akornsys-rdi/open-wound/brd/master/audio-sensing-board/audio.sch

## KiCad design brd/master/audio-sensing-board/audio.sch (2015-06-30)

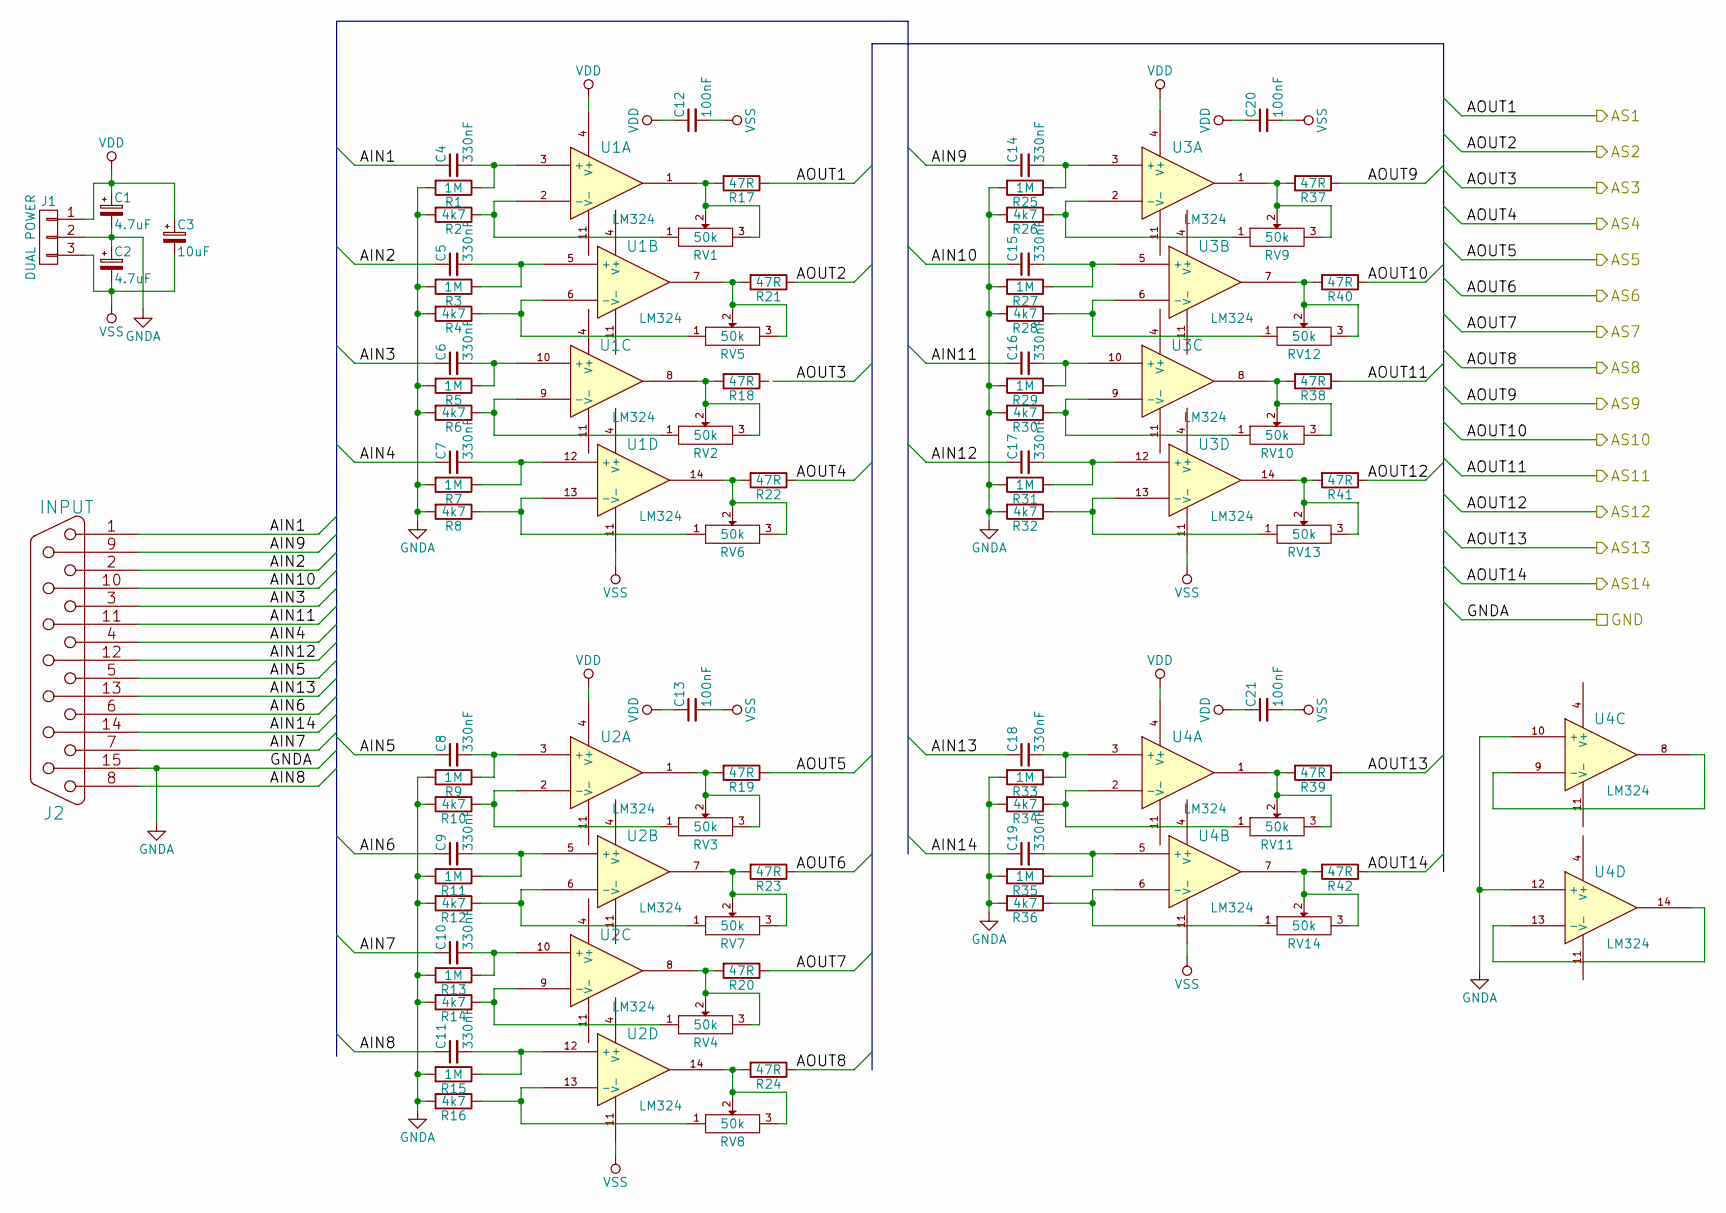
[picture p10: schematic audio.sch]

Parts:
C1, C2: 4.7uF
C3: 10uF
C4, C5, C6, C7, C8, C9, C10, C11, C14, C15, C16, C17, C18, C19: 330nF
C12, C13, C20, C21: 100nF
J1: DUAL POWER
J2: INPUT
R1, R3, R5, R7, R9, R11, R13, R15, R25, R27, R29, R31, R33, R35: 1M
R2, R4, R6, R8, R10, R12, R14, R16, R26, R28, R30, R32, R34, R36: 4k7
R17, R18, R19, R20, R21, R22, R23, R24, R37, R38, R39, R40, R41, R42: 47R
RV1, RV2, RV3, RV4, RV5, RV6, RV7, RV8, RV9, RV10, RV11, RV12, RV13, RV14: 50k
U1, U2, U3, U4: LM324

Connections:
AIN1: C4.1, J2.1
AIN2: C5.1, J2.2
AIN3: C6.1, J2.3
AIN4: C7.1, J2.4
AIN5: C8.1, J2.5
AIN6: C9.1, J2.6
AIN7: C10.1, J2.7
AIN8: C11.1, J2.8
AIN9: C14.1, J2.9
AIN10: C15.1, J2.10
AIN11: C16.1, J2.11 (P111)
AIN12: C17.1, J2.12
AIN13: C18.1, J2.13
AIN14: C19.1, J2.14
AOUT1: R17.1
AOUT2: R21.1
AOUT4: R22.1
AOUT5: R19.1
AOUT6: R23.1
AOUT7: R20.1
AOUT8: R24.1
AOUT9: R37.1
AOUT10: R40.1
AOUT11: R38.1
AOUT12: R41.1
AOUT13: R39.1
AOUT14: R42.1
GNDA: C1.2, C2.1, J1.2, J2.15, R1.2, R2.2, R3.2, R4.2, R5.2, R6.2, R7.2, R8.2, R9.2, R10.2, R11.2, R12.2, R13.2, R14.2, R15.2, R16.2, R25.2, R26.2, R27.2, R28.2, R29.2, R30.2, R31.2, R32.2, R33.2, R34.2, R35.2, R36.2, U4.10 (+), U4.12 (+)
unnamed: C4.2, R1.1, U1.3 (+)
unnamed: C5.2, R3.1, U1.5 (+)
unnamed: C6.2, R5.1, U1.10 (+)
unnamed: C7.2, R7.1, U1.12 (+)
unnamed: C8.2, R9.1, U2.3 (+)
unnamed: C9.2, R11.1, U2.5 (+)
unnamed: C10.2, R13.1, U2.10 (+)
unnamed: C11.2, R15.1, U2.12 (+)
unnamed: C14.2, R25.1, U3.3 (+)
unnamed: C15.2, R27.1, U3.5 (+)
unnamed: C16.2, R29.1, U3.10 (+)
unnamed: C17.2, R31.1, U3.12 (+)
unnamed: C18.2, R33.1, U4.3 (+)
unnamed: C19.2, R35.1, U4.5 (+)
unnamed: R2.1, RV1.1, U1.2 (-)
unnamed: R4.1, RV5.1, U1.6 (-)
unnamed: R6.1, RV2.1, U1.9 (-)
unnamed: R8.1, RV6.1, U1.13 (-)
unnamed: R10.1, RV3.1, U2.2 (-)
unnamed: R12.1, RV7.1, U2.6 (-)
unnamed: R14.1, RV4.1, U2.9 (-)
unnamed: R16.1, RV8.1, U2.13 (-)
unnamed: R17.2, RV1.2, RV1.3, U1.1
unnamed: R18.2, RV2.2, RV2.3, U1.8
unnamed: R19.2, RV3.2, RV3.3, U2.1
unnamed: R20.2, RV4.2, RV4.3, U2.8
unnamed: R21.2, RV5.2, RV5.3, U1.7
unnamed: R22.2, RV6.2, RV6.3, U1.14
unnamed: R23.2, RV7.2, RV7.3, U2.7
unnamed: R24.2, RV8.2, RV8.3, U2.14
unnamed: R26.1, RV9.1, U3.2 (-)
unnamed: R28.1, RV12.1, U3.6 (-)
unnamed: R30.1, RV10.1, U3.9 (-)
unnamed: R32.1, RV13.1, U3.13 (-)
unnamed: R34.1, RV11.1, U4.2 (-)
unnamed: R36.1, RV14.1, U4.6 (-)
unnamed: R37.2, RV9.2, RV9.3, U3.1
unnamed: R38.2, RV10.2, RV10.3, U3.8
unnamed: R39.2, RV11.2, RV11.3, U4.1
unnamed: R40.2, RV12.2, RV12.3, U3.7
unnamed: R41.2, RV13.2, RV13.3, U3.14
unnamed: R42.2, RV14.2, RV14.3, U4.7
unnamed: U4.8, U4.9 (-)
unnamed: U4.13 (-), U4.14
VDD: C1.1, C3.1, C12.1, C13.1, C20.1, C21.1, J1.1, U1.4 (V+), U2.4 (V+), U3.4 (V+), U4.4 (V+)
VSS: C2.2, C3.2, C12.2, C13.2, C20.2, C21.2, J1.3, U1.11 (V-), U2.11 (V-), U3.11 (V-), U4.11 (V-)
