akornsys-rdi/open-wound/brd/master/audio-sensing-board/digital.sch

## KiCad design brd/master/audio-sensing-board/digital.sch (2015-06-30)

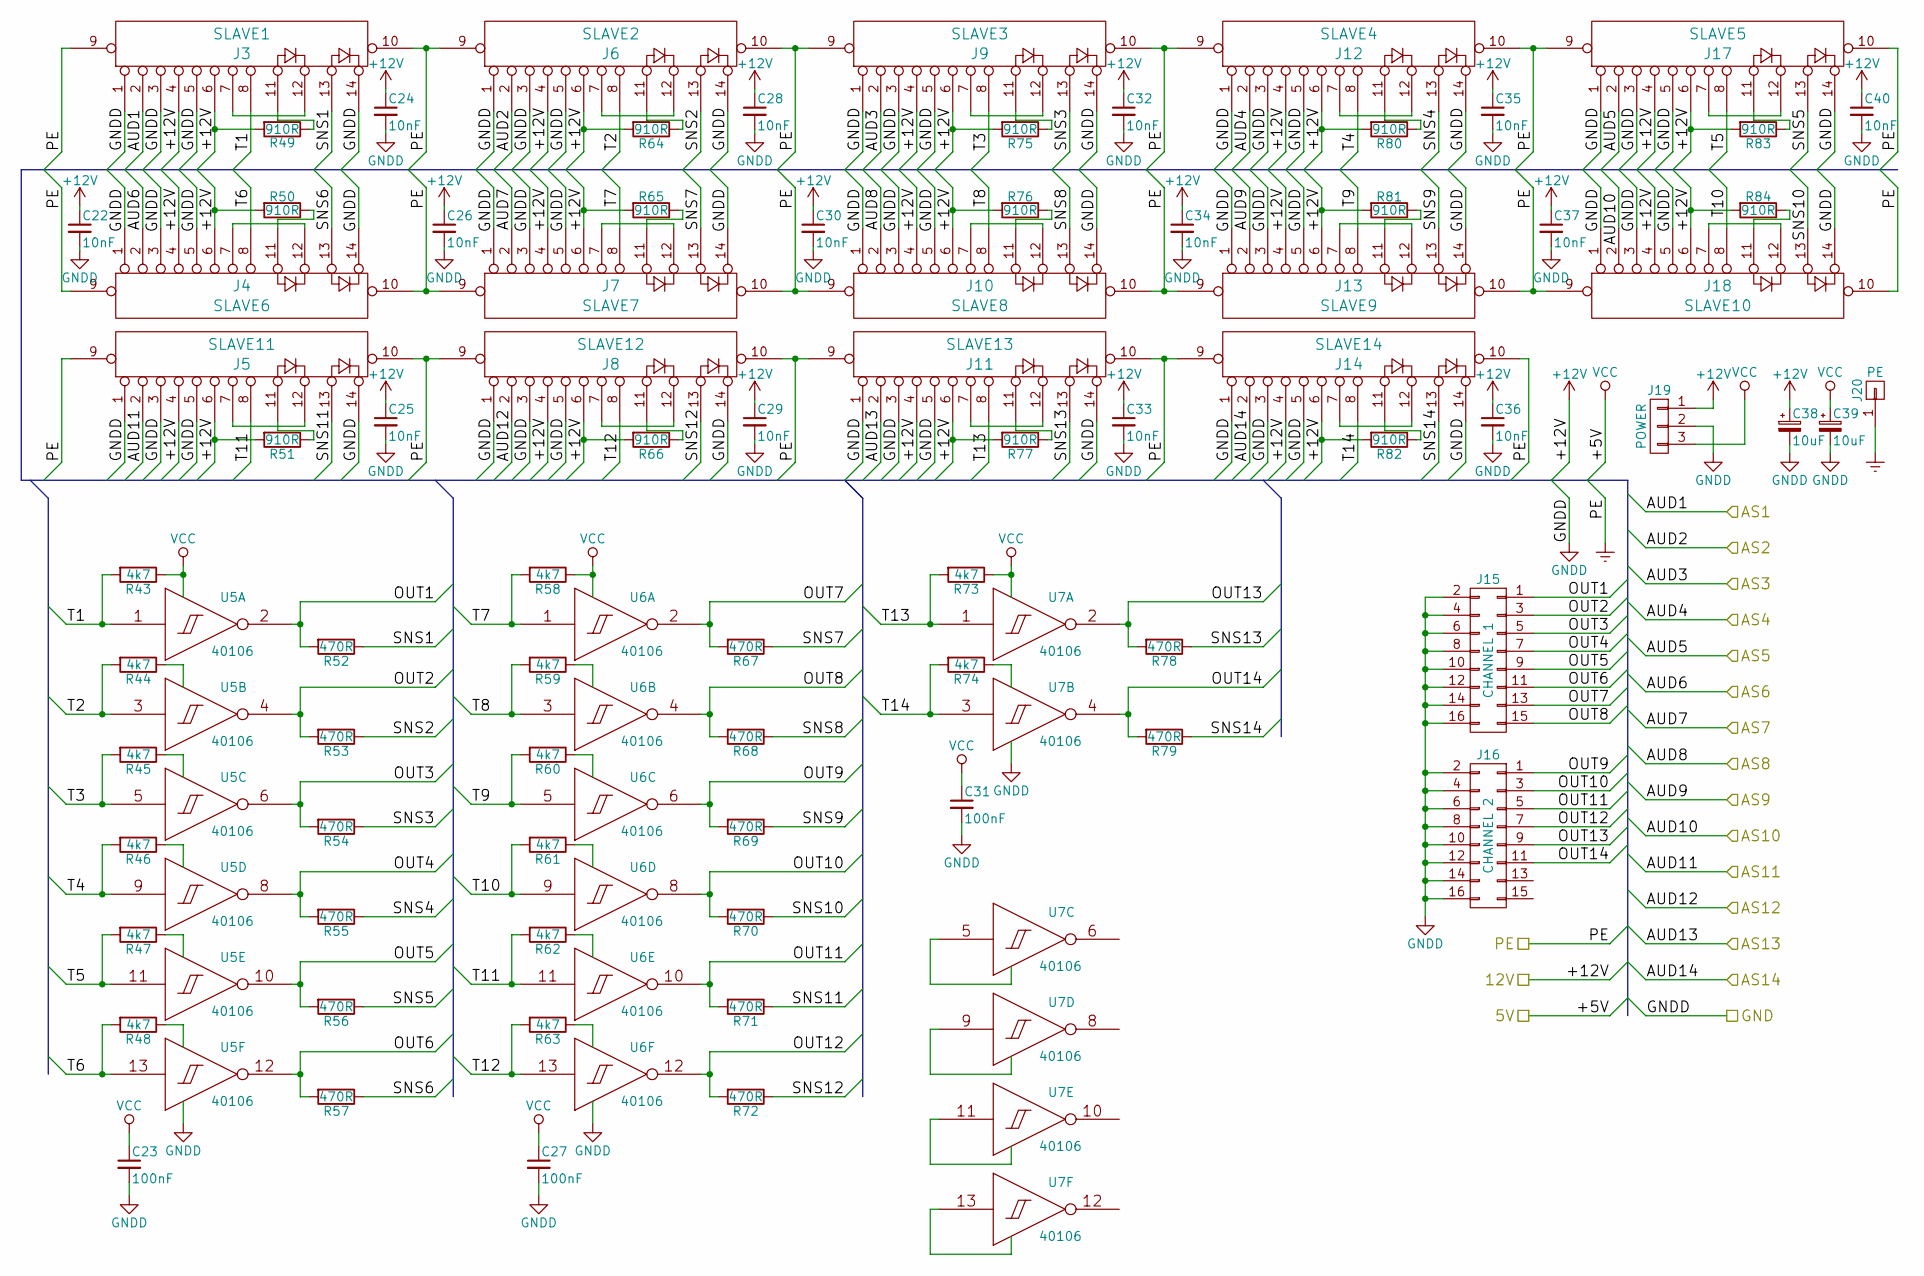
[picture p11: schematic digital.sch]

Parts:
C22, C24, C25, C26, C28, C29, C30, C32, C33, C34, C35, C36, C37, C40: 10nF
C23, C27, C31: 100nF
C38, C39: 10uF
J3: SLAVE1
J4: SLAVE6
J5: SLAVE11
J6: SLAVE2
J7: SLAVE7
J8: SLAVE12
J9: SLAVE3
J10: SLAVE8
J11: SLAVE13
J12: SLAVE4
J13: SLAVE9
J14: SLAVE14
J15: CHANNEL 1
J16: CHANNEL 2
J17: SLAVE5
J18: SLAVE10
J19: POWER
J20: PE
R43, R44, R45, R46, R47, R48, R58, R59, R60, R61, R62, R63, R73, R74: 4k7
R49, R50, R51, R64, R65, R66, R75, R76, R77, R80, R81, R82, R83, R84: 910R
R52, R53, R54, R55, R56, R57, R67, R68, R69, R70, R71, R72, R78, R79: 470R
U5, U6, U7: 40106

Connections:
+12V: C22.1, C24.1, C25.1, C26.1, C28.1, C29.1, C30.1, C32.1, C33.1, C34.1, C35.1, C36.1, C37.1, C38.1, C40.1, J3.4, J3.6, J4.4, J4.6, J5.4, J5.6, J6.4, J6.6, J7.4, J7.6, J8.4, J8.6, J9.4, J9.6, J10.4, J10.6, J11.4, J11.6, J12.4, J12.6, J13.4, J13.6, J14.4, J14.6, J17.4, J17.6, J18.4, J18.6, J19.1, R49.2, R50.2, R51.2, R64.2, R65.2, R66.2, R75.2, R76.2, R77.2, R80.2, R81.2, R82.2, R83.2, R84.2
AS1: J3.2
AS2: J6.2
AS3: J9.2
AS4: J12.2
AS5: J17.2
AS6: J4.2
AS7: J7.2
AS8: J10.2
AS9: J13.2
AS10: J18.2
AS11: J5.2
AS12: J8.2
AS13: J11.2
AS14: J14.2
Earth: J3.9, J3.10, J4.9, J4.10, J5.9, J5.10, J6.9, J6.10, J7.9, J7.10, J8.9, J8.10, J9.9, J9.10, J10.9, J10.10, J11.9, J11.10, J12.9, J12.10, J13.9, J13.10, J14.9, J14.10, J17.9, J17.10, J18.9, J18.10, J20.1
GNDD: C22.2, C23.2, C24.2, C25.2, C26.2, C27.2, C28.2, C29.2, C30.2, C31.2, C32.2, C33.2, C34.2, C35.2, C36.2, C37.2, C38.2, C39.2, C40.2, J3.1, J3.3, J3.5, J3.14, J4.1, J4.3, J4.5, J4.14, J5.1, J5.3, J5.5, J5.14, J6.1, J6.3, J6.5, J6.14, J7.1, J7.3, J7.5, J7.14, J8.1, J8.3, J8.5, J8.14, J9.1, J9.3, J9.5, J9.14, J10.1, J10.3, J10.5, J10.14, J11.1, J11.3, J11.5, J11.14, J12.1, J12.3, J12.5, J12.14, J13.1, J13.3, J13.5, J13.14, J14.1, J14.3, J14.5, J14.14, J15.2, J15.4, J15.6, J15.8, J15.10, J15.12, J15.14, J15.16, J16.2, J16.4, J16.6, J16.8, J16.10, J16.12, J16.14, J16.16, J17.1, J17.3, J17.5, J17.14, J18.1, J18.3, J18.5, J18.14, J19.2, U5.7 (VSS), U6.7 (VSS), U7.7 (VSS)
unnamed: J3.11, R49.1
unnamed: J3.7, J3.12
unnamed: J4.11, R50.1
unnamed: J4.7, J4.12
unnamed: J5.11, R51.1
unnamed: J5.7, J5.12
unnamed: J6.11, R64.1
unnamed: J6.7, J6.12
unnamed: J7.11, R65.1
unnamed: J7.7, J7.12
unnamed: J8.11, R66.1
unnamed: J8.7, J8.12
unnamed: J9.11, R75.1
unnamed: J9.7, J9.12
unnamed: J10.11, R76.1
unnamed: J10.7, J10.12
unnamed: J11.11, R77.1
unnamed: J11.7, J11.12
unnamed: J12.11, R80.1
unnamed: J12.7, J12.12
unnamed: J13.11, R81.1
unnamed: J13.7, J13.12
unnamed: J14.11, R82.1
unnamed: J14.7, J14.12
unnamed: J17.11, R83.1
unnamed: J17.7, J17.12
unnamed: J18.11, R84.1
unnamed: J18.7, J18.12
unnamed: R44.1, U5.14 (VDD)
unnamed: R45.1, U5.14 (VDD)
unnamed: R46.1, U5.14 (VDD)
unnamed: R47.1, U5.14 (VDD)
unnamed: R48.1, U5.14 (VDD)
unnamed: R59.1, U6.14 (VDD)
unnamed: R60.1, U6.14 (VDD)
unnamed: R61.1, U6.14 (VDD)
unnamed: R62.1, U6.14 (VDD)
unnamed: R63.1, U6.14 (VDD)
unnamed: R74.1, U7.14 (VDD)
unnamed: U7.5 (In), U7.7 (VSS)
unnamed: U7.7 (VSS), U7.9 (In)
unnamed: U7.7 (VSS), U7.11 (In)
unnamed: U7.7 (VSS), U7.13 (In)
OUT1: J15.1, R52.2, U5.2 (Out)
OUT2: J15.3, R53.2, U5.4 (Out)
OUT3: J15.5, R54.2, U5.6 (Out)
OUT4: J15.7, R55.2, U5.8 (Out)
OUT5: J15.9, R56.2, U5.10 (Out)
OUT6: J15.11, R57.2, U5.12 (Out)
OUT7: J15.13, R67.2, U6.2 (Out)
OUT8: J15.15, R68.2, U6.4 (Out)
OUT9: J16.1, R69.2, U6.6 (Out)
OUT10: J16.3, R70.2, U6.8 (Out)
OUT11: J16.5, R71.2, U6.10 (Out)
OUT12: J16.7, R72.2, U6.12 (Out)
OUT13: J16.9, R78.2, U7.2 (Out)
OUT14: J16.11, R79.2, U7.4 (Out)
SNS1: J3.13, R52.1
SNS2: J6.13, R53.1
SNS3: J9.13, R54.1
SNS4: J12.13, R55.1
SNS5: J17.13, R56.1
SNS6: J4.13, R57.1
SNS7: J7.13, R67.1
SNS8: J10.13, R68.1
SNS9: J13.13, R69.1
SNS10: J18.13, R70.1
SNS11: J5.13, R71.1
SNS12: J8.13, R72.1
SNS13: J11.13, R78.1
SNS14: J14.13, R79.1
T1: J3.8, R43.2, U5.1 (In)
T2: J6.8, R44.2, U5.3 (In)
T3: J9.8, R45.2, U5.5 (In)
T4: J12.8, R46.2, U5.9 (In)
T5: J17.8, R47.2, U5.11 (In)
T6: J4.8, R48.2, U5.13 (In)
T7: J7.8, R58.2, U6.1 (In)
T8: J10.8, R59.2, U6.3 (In)
T9: J13.8, R60.2, U6.5 (In)
T10: J18.8, R61.2, U6.9 (In)
T11: J5.8, R62.2, U6.11 (In)
T12: J8.8, R63.2, U6.13 (In)
T13: J11.8, R73.2, U7.1 (In)
T14: J14.8, R74.2, U7.3 (In)
VCC: C23.1, C27.1, C31.1, C39.1, J19.3, R43.1, R58.1, R73.1, U5.14 (VDD), U6.14 (VDD), U7.14 (VDD)
