akornsys-rdi/open-wound/brd/master/audio-sensing-board/pir.sch

## KiCad design brd/master/audio-sensing-board/pir.sch (2015-06-30)

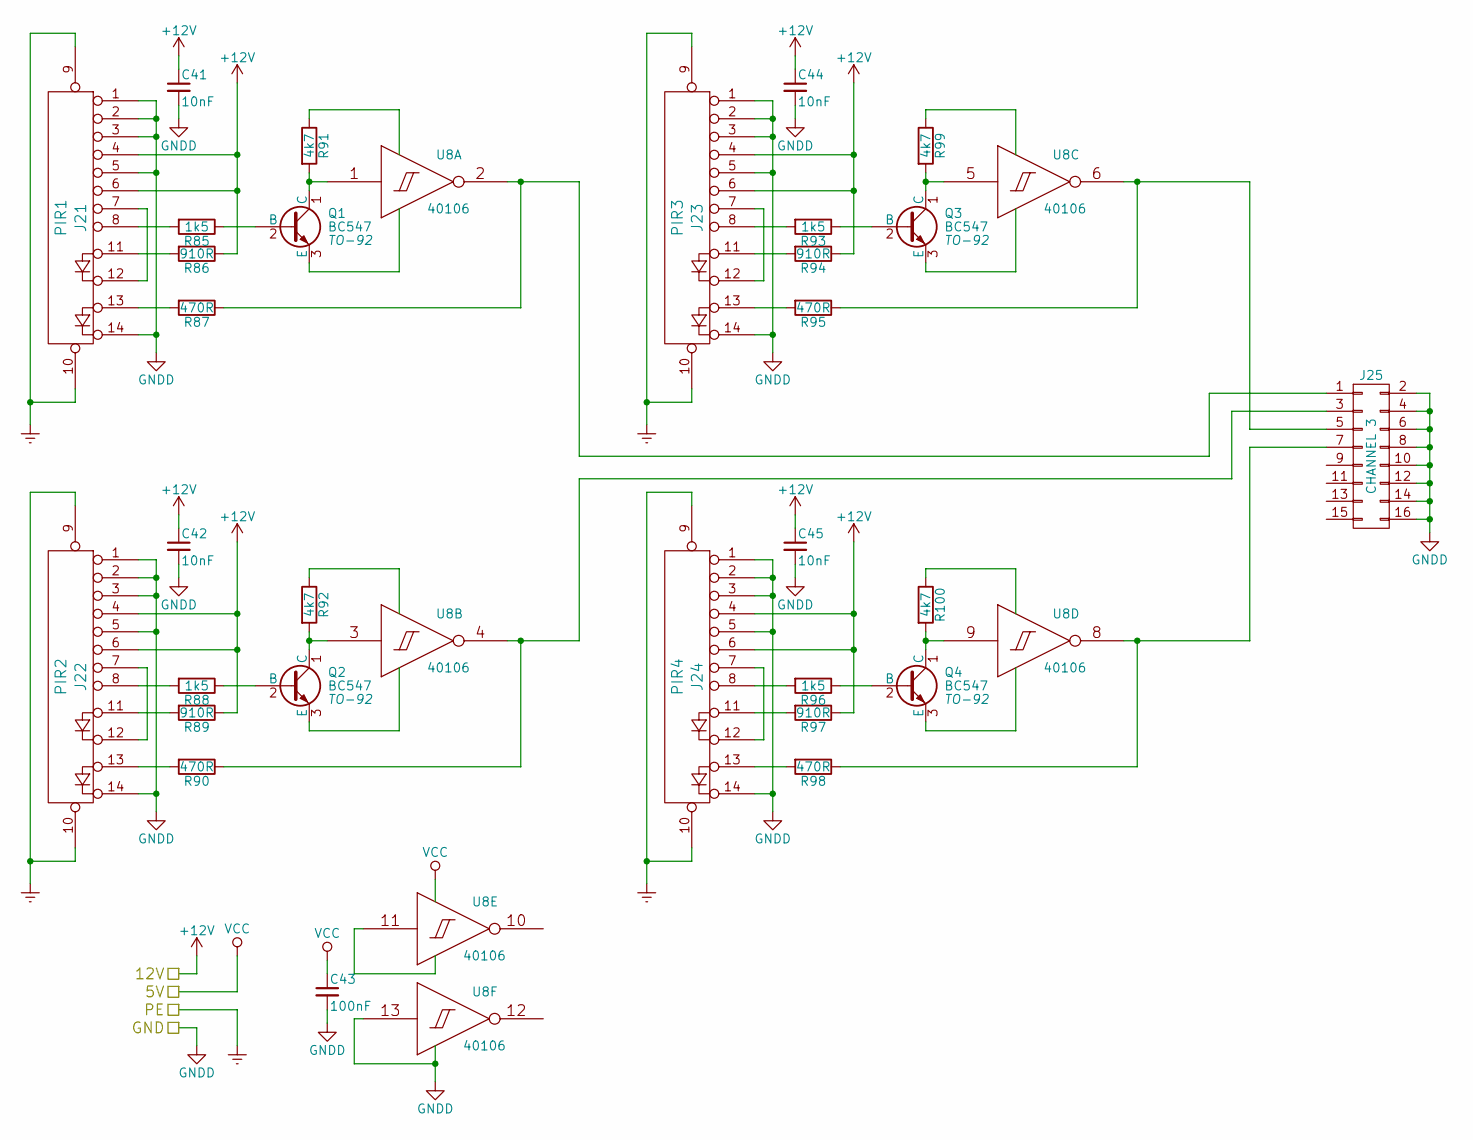
[picture p12: schematic pir.sch]

Parts:
C41, C42, C44, C45: 10nF
C43: 100nF
J21: PIR1
J22: PIR2
J23: PIR3
J24: PIR4
J25: CHANNEL 3
Q1, Q2, Q3, Q4: BC547; TO-92
R85, R88, R93, R96: 1k5
R86, R89, R94, R97: 910R
R87, R90, R95, R98: 470R
R91, R92, R99, R100: 4k7
U8: 40106

Connections:
+12V: C41.1, C42.1, C44.1, C45.1, J21.4, J21.6, J22.4, J22.6, J23.4, J23.6, J24.4, J24.6, R86.1, R89.1, R94.1, R97.1
Earth: J21.9, J21.10, J22.9, J22.10, J23.9, J23.10, J24.9, J24.10
GNDD: C41.2, C42.2, C43.2, C44.2, C45.2, J21.1, J21.2, J21.3, J21.5, J21.14, J22.1, J22.2, J22.3, J22.5, J22.14, J23.1, J23.2, J23.3, J23.5, J23.14, J24.1, J24.2, J24.3, J24.5, J24.14, J25.2, J25.4, J25.6, J25.8, J25.10, J25.12, J25.14, J25.16, U8.7 (VSS), U8.13 (In)
unnamed: J21.8, R85.2
unnamed: J21.11, R86.2
unnamed: J21.7, J21.12
unnamed: J21.13, R87.2
unnamed: J22.8, R88.2
unnamed: J22.11, R89.2
unnamed: J22.7, J22.12
unnamed: J22.13, R90.2
unnamed: J23.8, R93.2
unnamed: J23.11, R94.2
unnamed: J23.7, J23.12
unnamed: J23.13, R95.2
unnamed: J24.8, R96.2
unnamed: J24.11, R97.2
unnamed: J24.7, J24.12
unnamed: J24.13, R98.2
unnamed: J25.1, R87.1, U8.2 (Out)
unnamed: J25.3, R90.1, U8.4 (Out)
unnamed: J25.5, R95.1, U8.6 (Out)
unnamed: J25.7, R98.1, U8.8 (Out)
unnamed: Q1.1 (C), R91.2, U8.1 (In)
unnamed: Q1.2 (B), R85.1
unnamed: Q1.3 (E), U8.7 (VSS)
unnamed: Q2.1 (C), R92.2, U8.3 (In)
unnamed: Q2.2 (B), R88.1
unnamed: Q2.3 (E), U8.7 (VSS)
unnamed: Q3.1 (C), R99.2, U8.5 (In)
unnamed: Q3.2 (B), R93.1
unnamed: Q3.3 (E), U8.7 (VSS)
unnamed: Q4.1 (C), R100.2, U8.9 (In)
unnamed: Q4.2 (B), R96.1
unnamed: Q4.3 (E), U8.7 (VSS)
unnamed: R91.1, U8.14 (VDD)
unnamed: R92.1, U8.14 (VDD)
unnamed: R99.1, U8.14 (VDD)
unnamed: R100.1, U8.14 (VDD)
unnamed: U8.7 (VSS), U8.11 (In)
VCC: C43.1, U8.14 (VDD)
